eta4ever/dimmer485/hardware/encoder.sch

## EAGLE design hardware/encoder.sch (2015-07-19)

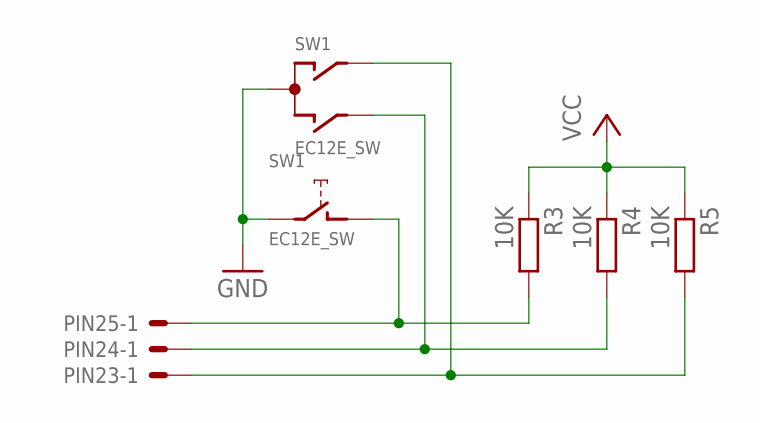
[picture p3: schematic encoder.sch]

Parts:
PIN23, PIN24, PIN25: 5566-10
R3, R4, R5: 10K; M1206
SW1: EC12E_SW; ALPS_EC12E_SW

Connections:
GND: SW1.C, SW1.E (2)
unnamed: PIN23.1, R5.2, SW1.A
unnamed: PIN24.1, R4.2, SW1.B
unnamed: PIN25.1, R3.2, SW1.D (1)
VCC: R3.1, R4.1, R5.1
