eta4ever/dimmer485/hardware/led driver.sch

## EAGLE design hardware/led driver.sch (2015-07-19)

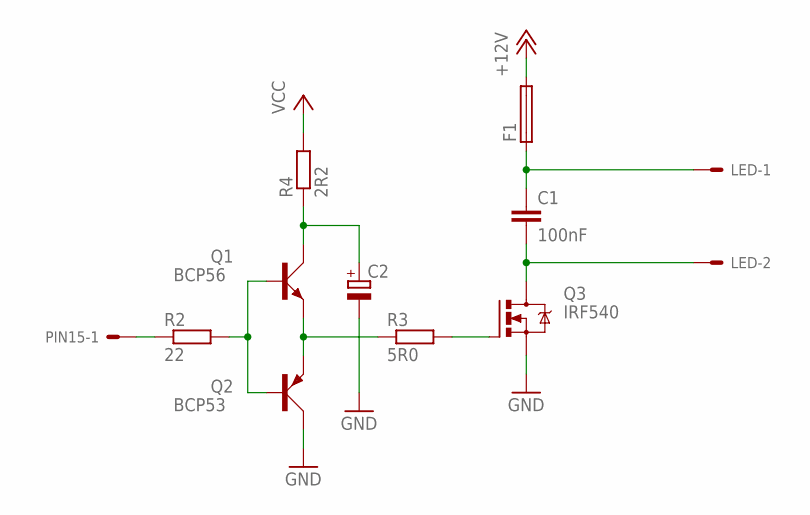
[picture p4: schematic led driver.sch]

Parts:
C1: 100nF; C2.5-3
C2: CPOL-EU085CS-1AR; 085CS_1AR
F1: TE5
LED: 5566-10
PIN15: 5566-10
Q1: BCP56; SOT54D
Q2: BCP53; SOT54D
Q3: IRF540; TO220BV
R2: 22; R1206
R3: 5R0; R1206
R4: 2R2; R1206

Connections:
+12V: F1.2
GND: C2.-, Q2.C, Q3.S
unnamed: Q1.B, Q2.B, R2.2
unnamed: PIN15.1, R2.1
unnamed: Q1.E, Q2.E, R3.1
unnamed: Q3.G, R3.2
unnamed: C1.2, LED.2, Q3.D
unnamed: C2.+, Q1.C, R4.1
unnamed: C1.1, F1.1, LED.1
VCC: R4.2
