eta4ever/dimmer485/hardware/main.sch

## EAGLE design hardware/main.sch (2015-07-15)

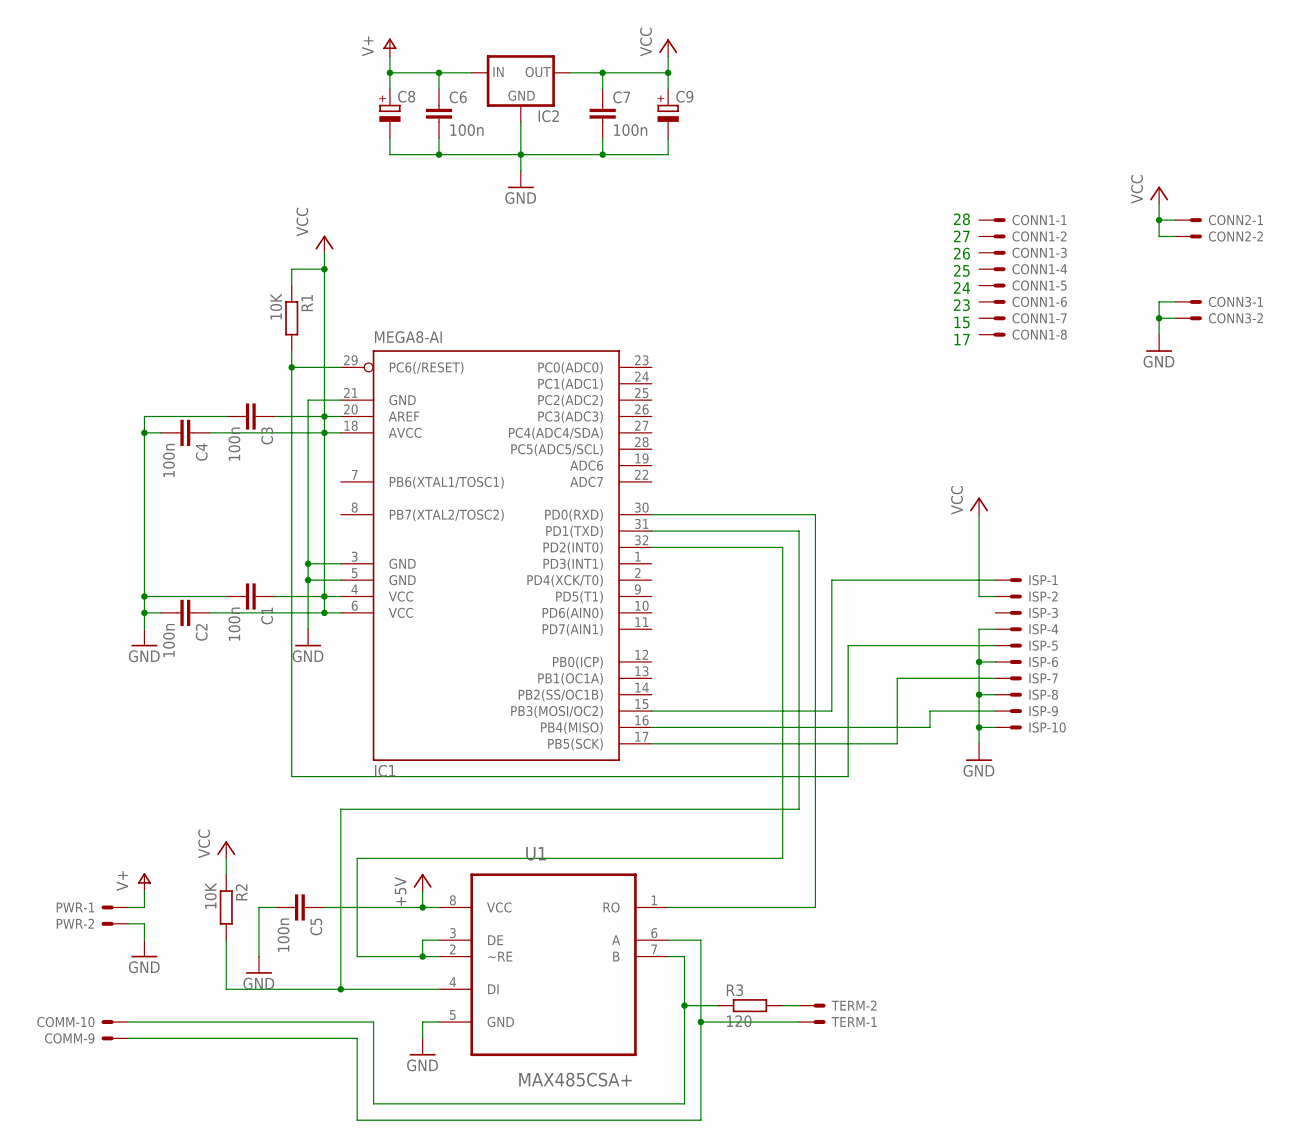
[picture p5: schematic main.sch]

Parts:
C1, C2, C3, C4, C5, C6, C7: 100n; C2.5-3
C8, C9: CPOL-EU085CS-1AR; 085CS_1AR
COMM: 5566-10
CONN1, CONN2, CONN3: 5566-10
IC1: MEGA8-AI; TQFP32-08
IC2: 78LXX
ISP: 5566-10
PWR: 5566-10
R1, R2: 10K; M1206
R3: 120; M1206
TERM: 5566-10
U1: MAX485CSA+; SOIC127P600X175-8N

Connections:
+5V: C5.1, U1.8 (VCC)
GND: C1.2, C2.2, C3.2, C4.2, C5.2, C6.2, C7.2, C8.-, C9.-, CONN3.1, CONN3.2, IC1.3 (GND), IC1.5 (GND), IC1.21 (GND), IC2.GND, ISP.4, ISP.6, ISP.8, ISP.10, PWR.2, U1.5 (GND)
unnamed: IC1.31 (PD1(TXD)), R2.2, U1.4 (DI)
unnamed: IC1.30 (PD0(RXD)), U1.1 (RO)
unnamed: IC1.32 (PD2(INT0)), U1.2 (~RE), U1.3 (DE)
unnamed: IC1.17 (PB5(SCK)), ISP.7
unnamed: COMM.10, R3.1, U1.7 (B)
unnamed: IC1.15 (PB3(MOSI/OC2)), ISP.1
unnamed: IC1.16 (PB4(MISO)), ISP.9
unnamed: COMM.9, TERM.1, U1.6 (A)
unnamed: R3.2, TERM.2
unnamed: IC1.29 (PC6(/RESET)), ISP.5, R1.2
V+: C6.1, C8.+, IC2.IN, PWR.1
VCC: C1.1, C2.1, C3.1, C4.1, C7.1, C9.+, CONN2.1, CONN2.2, IC1.4 (VCC), IC1.6 (VCC), IC1.18 (AVCC), IC1.20 (AREF), IC2.OUT, ISP.2, R1.1, R2.1

Notes on the sheet:
28 27 26 25 24 23 15 17
